joechiboo/3d-modeling/label-parts/photos/module_in_bag.jpg

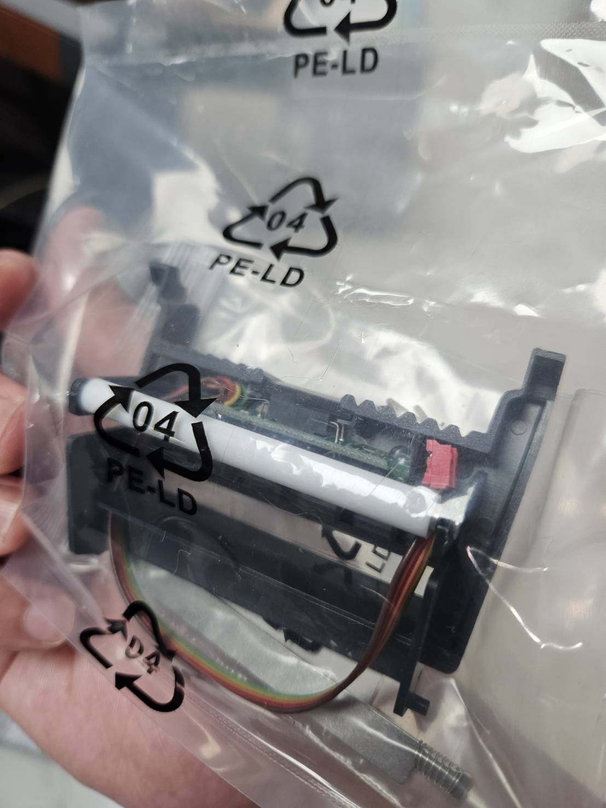
label-parts/photos/module_in_bag.jpg
