joechiboo/3d-modeling/label-parts/photos/peeler_inner_top.jpg

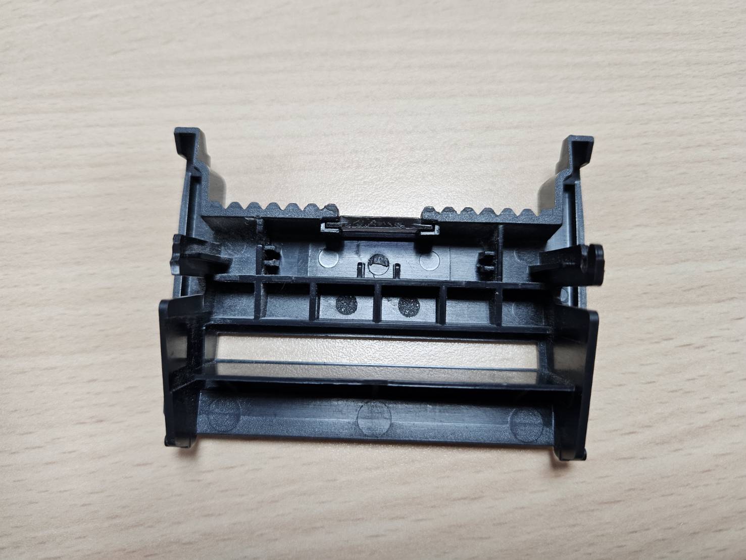
label-parts/photos/peeler_inner_top.jpg
