joechiboo/3d-modeling/label-parts/photos/peeler_inner_top_ruler.jpg

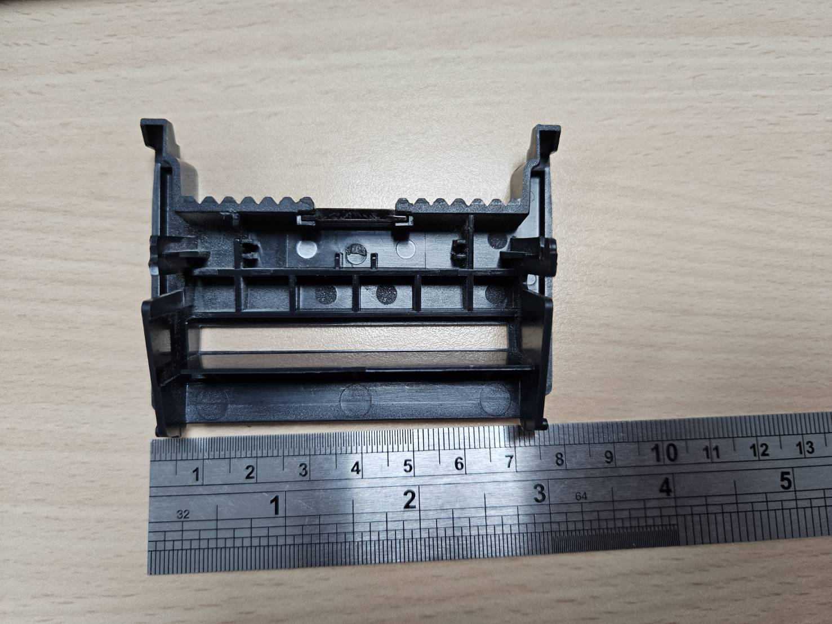
label-parts/photos/peeler_inner_top_ruler.jpg
