joechiboo/3d-modeling/label-parts/photos/peeler_outer_front.jpg

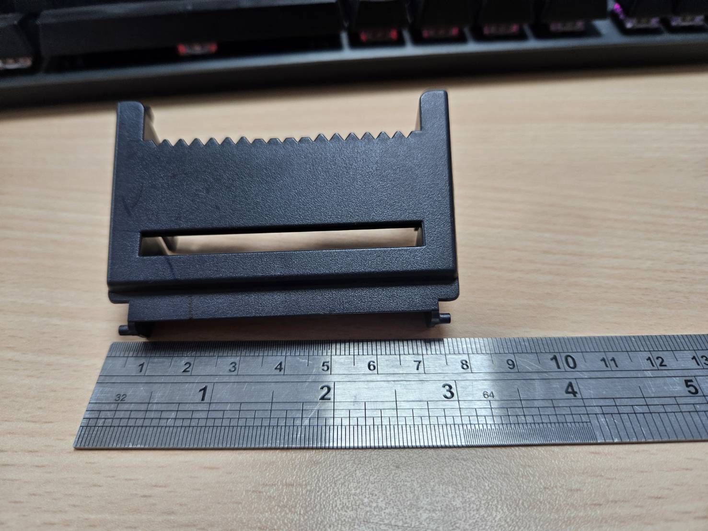
label-parts/photos/peeler_outer_front.jpg
