joechiboo/3d-modeling/label-parts/photos/peeler_outer_oblique_ruler.jpg

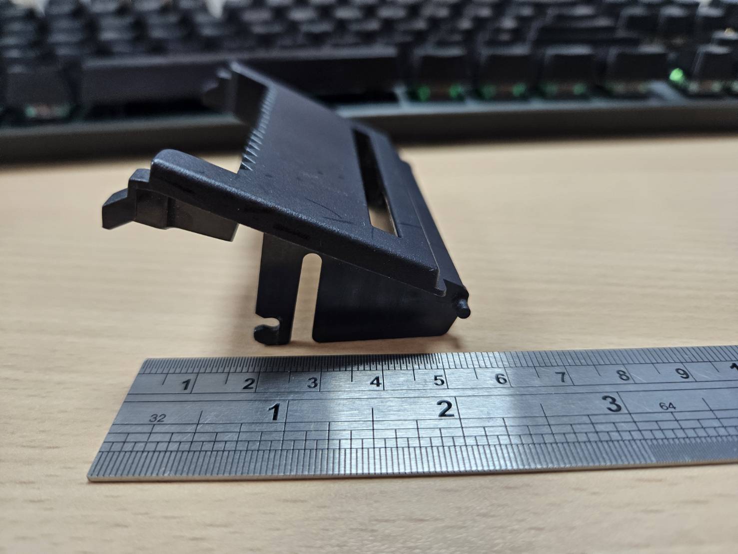
label-parts/photos/peeler_outer_oblique_ruler.jpg
