joechiboo/3d-modeling/label-parts/photos/peeler_outer_top.jpg

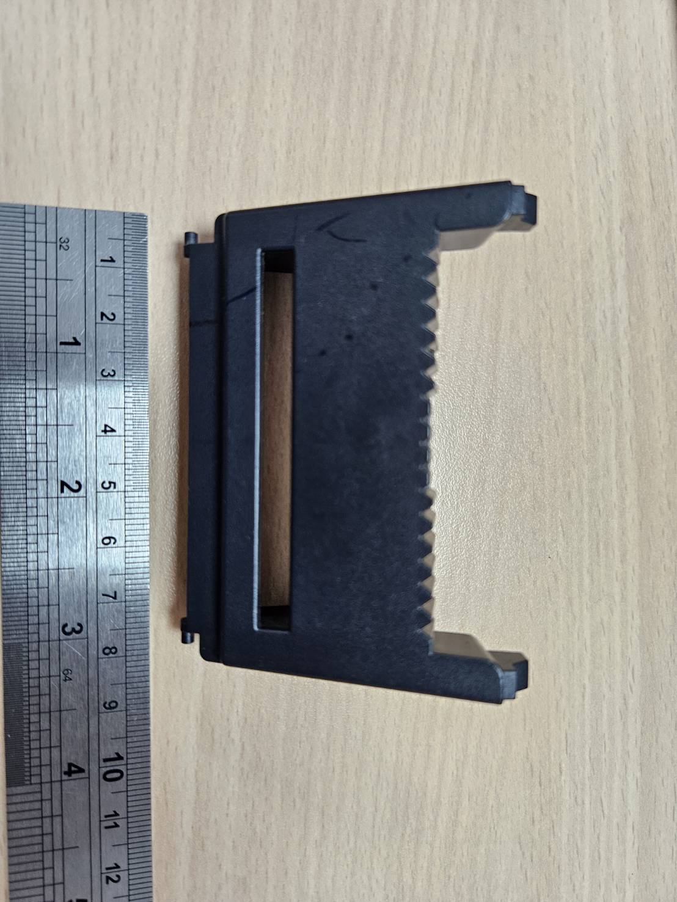
label-parts/photos/peeler_outer_top.jpg
