joechiboo/3d-modeling/label-parts/photos/peeler_side_hook.jpg

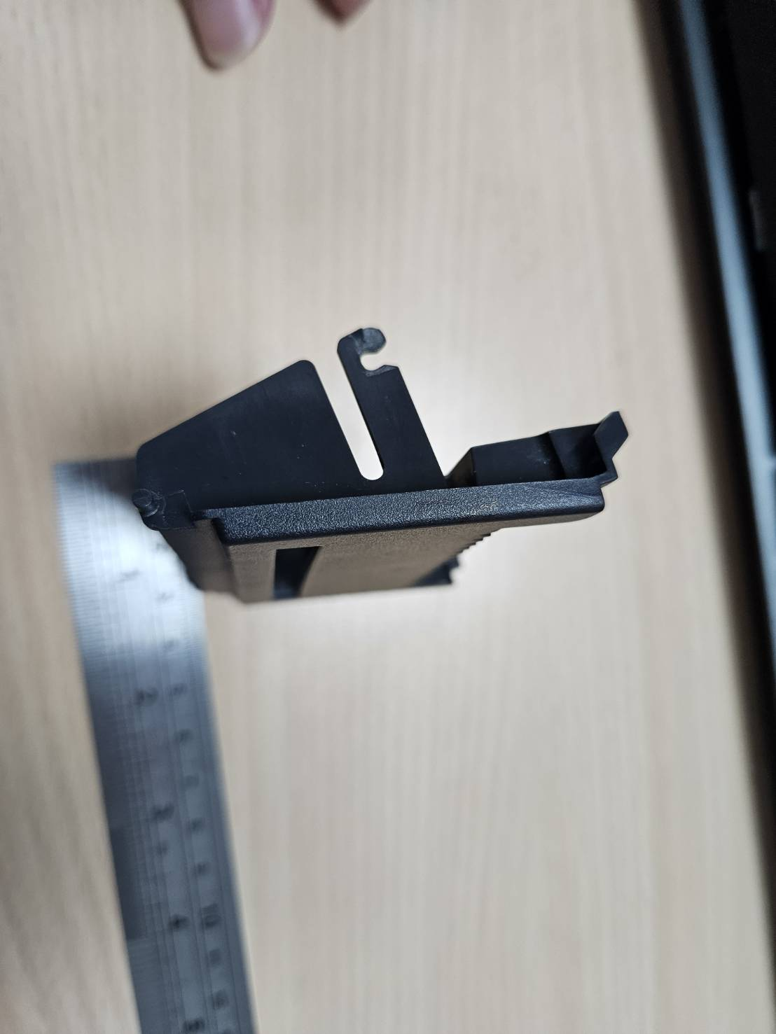
label-parts/photos/peeler_side_hook.jpg
