joechiboo/3d-modeling/label-parts/photos/module_printhead_inner.jpg

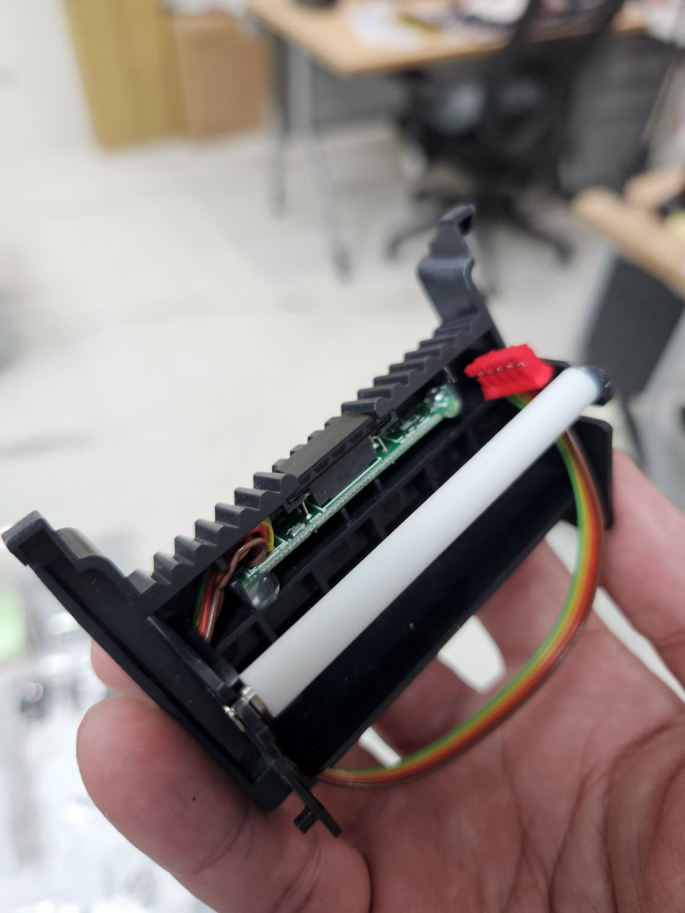
label-parts/photos/module_printhead_inner.jpg
